eipar/automotor/Documentation/CAN/can_send.png

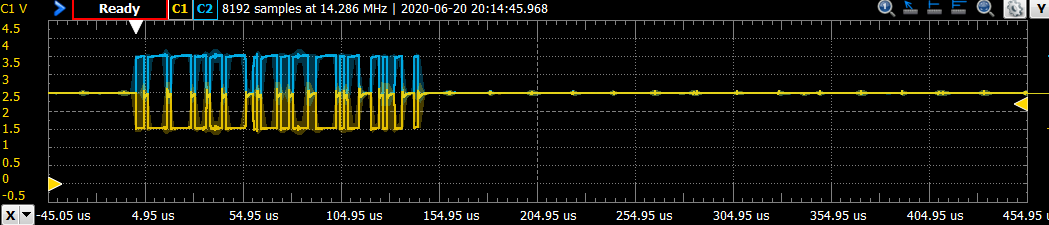
Documentation/CAN/can_send.png
