eipar/automotor/Documentation/CAN/can_send_acc.png

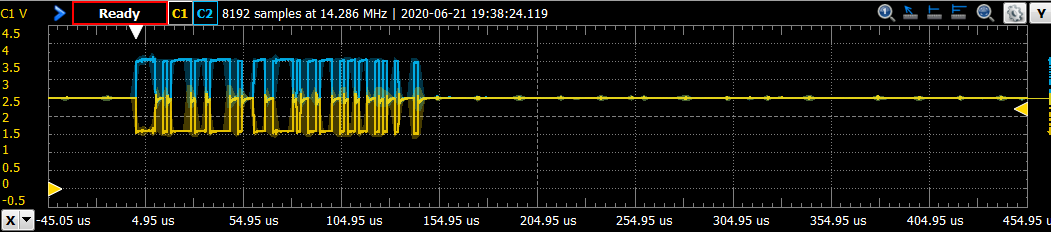
Documentation/CAN/can_send_acc.png
