eipar/automotor/Documentation/LIN/lin_read.png

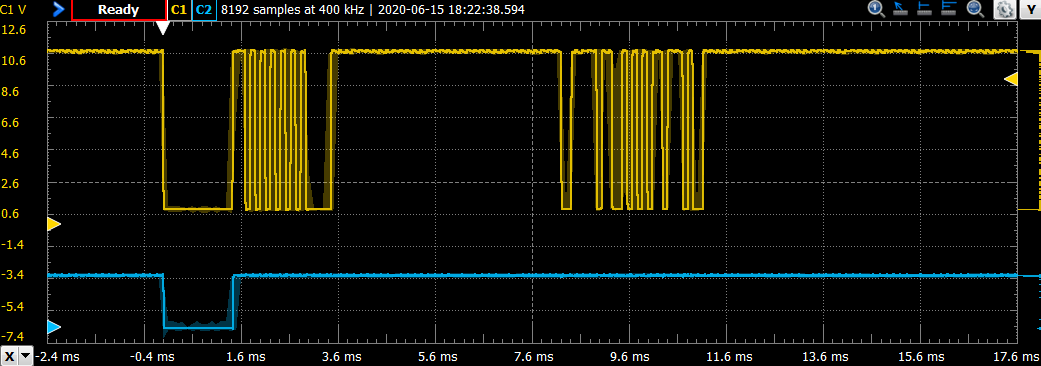
Documentation/LIN/lin_read.png
