eipar/automotor/Documentation/Motor/V_DC_Motor_y_Corriente.png

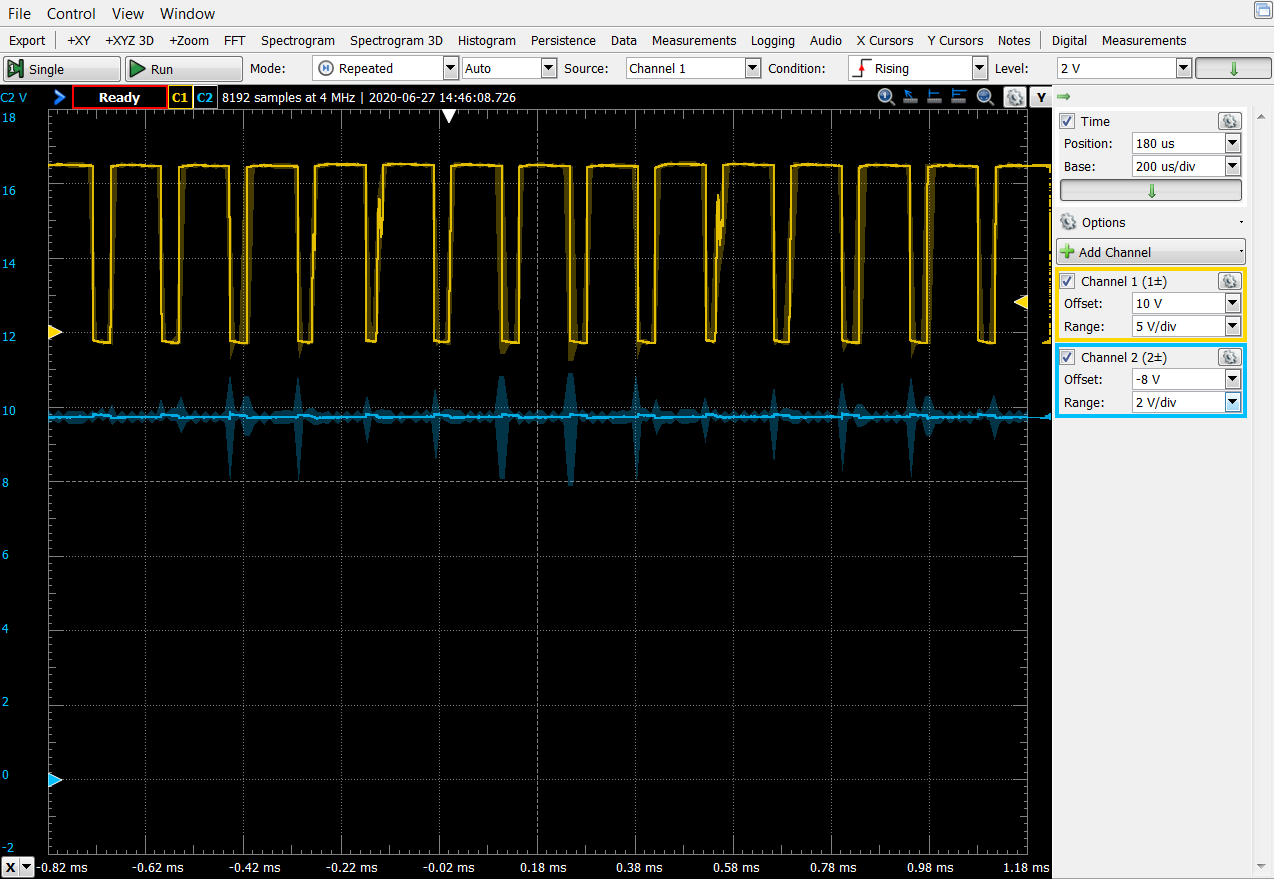
Documentation/Motor/V_DC_Motor_y_Corriente.png
