eipar/automotor/Documentation/Motor/V_DC_Motor_y_Feedback.png

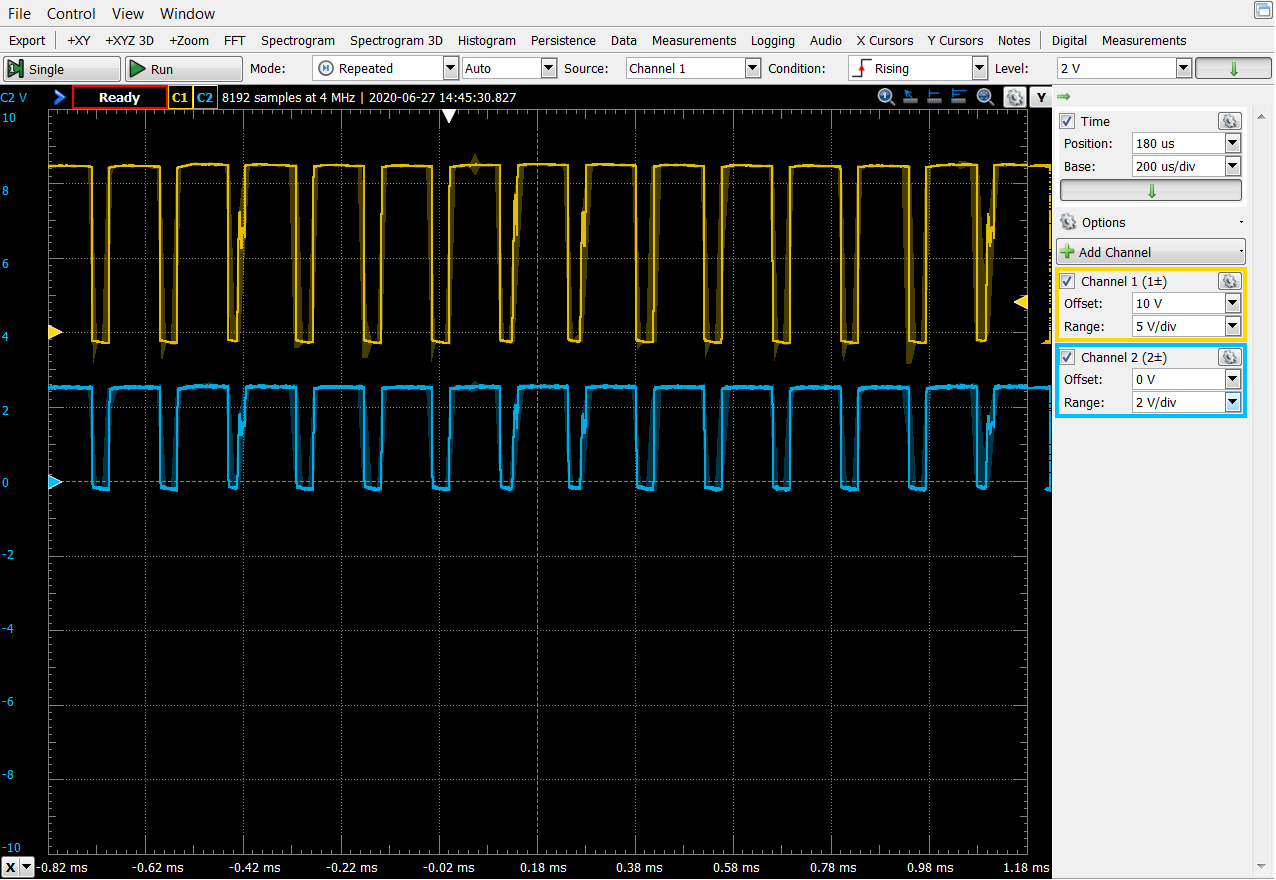
Documentation/Motor/V_DC_Motor_y_Feedback.png
