eipar/automotor/Documentation/Motor/V_en_DC_Motor.PNG

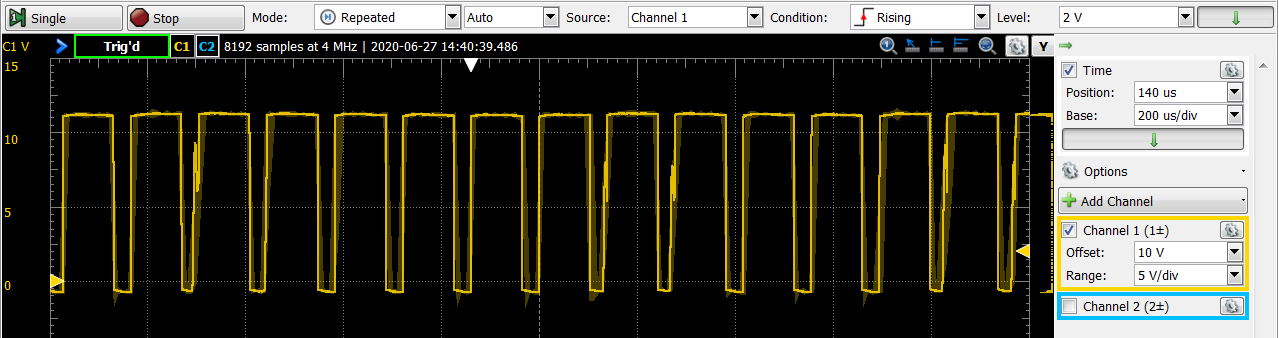
Documentation/Motor/V_en_DC_Motor.PNG
