eipar/automotor/Documentation/Motor_Modified/V_DC_Motor_y_Corriente.png

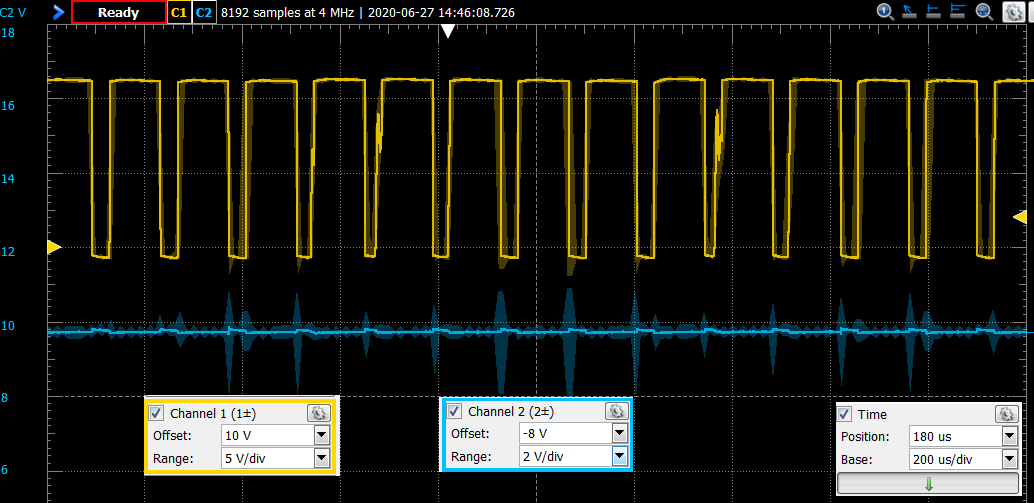
Documentation/Motor_Modified/V_DC_Motor_y_Corriente.png
