eipar/automotor/Documentation/Motor_Modified/V_en_DC_Motor.png

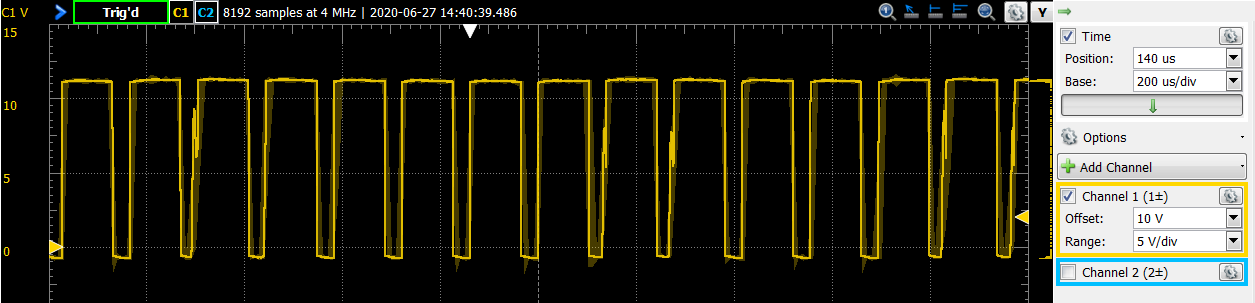
Documentation/Motor_Modified/V_en_DC_Motor.png
