eipar/automotor/Documentation/Motor_Modified/V_PWM.png

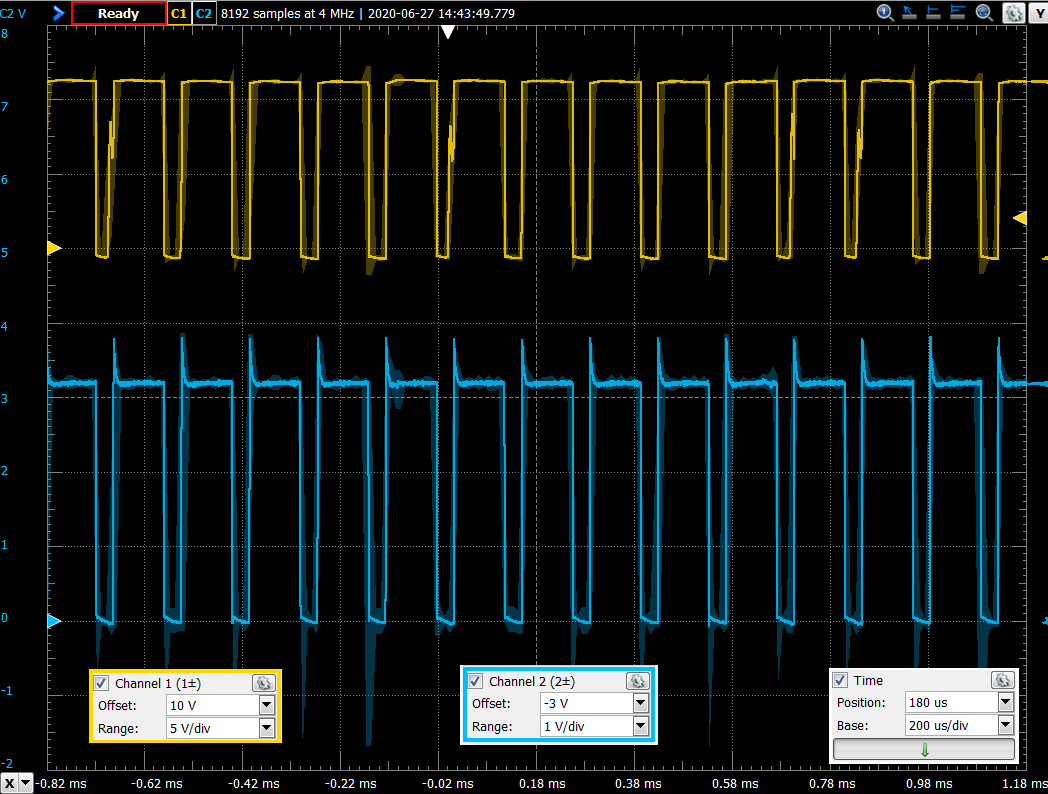
Documentation/Motor_Modified/V_PWM.png
