eipar/automotor/Simulation/sensadocorriente.asc

C1: cap; 100n
C2: cap; 10µ
C4: cap; 1m
D1: diode; MUR460
I1: current; PULSE(0.8 1 0 0.5m 0.5m 0 1m 1000)
R1: res; 10K
R2: res; 1K
R3: res; 10k
R4: res; 100
R5: res; 10k
Rshunt: res; 0.1
U1: opamp2; LM324/NS
V1: voltage; 12
Named nets: 0, V0, V+, V-, Vout, Vo_AC
.tran 0 50ms 0 1us
.inc LM324.mod
