eipar/automotor/Simulation/cont+sens.asc

C1: cap; 47n
C2: cap; 100n
C3: cap; 10µ
C4: cap; 2µ
D1: diode; 1N4148
D2: zener; 1N750
D3: diode; 1N4148
D4: diode; 1N4148
D5: diode; 1N4148
L1: ind; 10.6m
M1: nmos; IRFZ44N
M2: nmos; IRFZ44N
M3: nmos; 2N7002
M4: nmos; 2N7002
Q1: npn; BC547C
Q2: npn; BC547B
Q3: pnp; BC557B
Q4: pnp; BC557B
R1: res; 10k
R2: res; 1k
R3: res; 1k
R4: res; 10
R5: res; 30k
R6: res; 10k
R7: res; 10k
R8: res; 10
R9: res; 0.1
R10: res; 4.6
R11: res; 1k
R12: res; 10k
R13: res; 200
R14: res; 10k
R15: res; 10k
U1: opamp2; TL061
V1: voltage; PULSE(0 3.3 0 0.00001 0.00001 0.0003 0.0005 100)
V2: voltage; 12
V3: voltage; 3.3
V4: voltage; 3.3
V6: voltage; 12
Named nets: 0, VDD, Vfcontr, PWM, Vout, Vfreno, Vsens, Vcont, Vsens_amp, out_oa, orig_out
.tran 0 100m 0 100n
.inc "TL061.mod"
