eipar/automotor/Simulation/controlador.asc

C1: cap; 47n
D1: diode; 1N4148
D2: zener; 1N750
D3: diode; 1N4148
D4: diode; 1N4148
L1: ind; 10.6m
M1: nmos; IRFZ44N
M2: nmos; IRFZ44N
M3: nmos; 2N7002
M4: nmos; 2N7002
Q1: npn; BC547C
Q2: npn; BC547B
Q3: pnp; BC557B
Q4: pnp; BC557B
R1: res; 10k
R2: res; 1k
R3: res; 1k
R4: res; 10
R5: res; 30k
R6: res; 10k
R7: res; 10k
R8: res; 10
R9: res; 0.1
R10: res; 4.6
V1: voltage; PULSE(0 3.3 0.02 0.00001 0.00001 0.0004 0.001 100)
V2: voltage; 12
V3: voltage; 3.3
V4: voltage; 3.3
V5: voltage; PULSE(0 3.3 0.02 0.00001 0.00001 0.04 0.1 100)
Named nets: 0, VDD, Vfcontr, PWM, Vout, Vfreno, Vsens, NOT_PWM, Vcont
.tran 0 100m 0 100n
