eipar/automotor/8051/ntcm12.h

#ifndef		NTCM12_H
#define		NTCM12_H

//===============================================================================================
// Sensor de presion lineal - MPX6115A
//===============================================================================================
//-----------------------------------------------------------------------------------------------
// Includes
//-----------------------------------------------------------------------------------------------
#include <C8051F020.h>
//-----------------------------------------------------------------------------------------------
// Defines
//-----------------------------------------------------------------------------------------------
#define		MUESTRAS			20
#define     INTERVALO           22
//-----------------------------------------------------------------------------------------------
// Macros
//-----------------------------------------------------------------------------------------------

//-----------------------------------------------------------------------------------------------
// Entradas/Salidas
//-----------------------------------------------------------------------------------------------
sfr16		ADC0		=	0xBE;
//-----------------------------------------------------------------------------------------------
// Buffers
//-----------------------------------------------------------------------------------------------
#ifdef		DRIVER_NTCM12
	xdata volatile int buff_temp[ MUESTRAS ];
#else
#ifndef		APLICACION
	extern xdata volatile int buff_temp[ MUESTRAS ];
#endif
#endif
//-----------------------------------------------------------------------------------------------
// Prototipos de funciones
//-----------------------------------------------------------------------------------------------
float		LeerTemp		( void );		// Primitiva
float    TablaNTC        ( long );
//===============================================================================================

#endif		/* NTCM12_H */
